peterweissig/project_anhaenger/Skizzen/01_sweethome/export/2020_01_22/gerendert/Ansicht_von_Aussen2.jpg

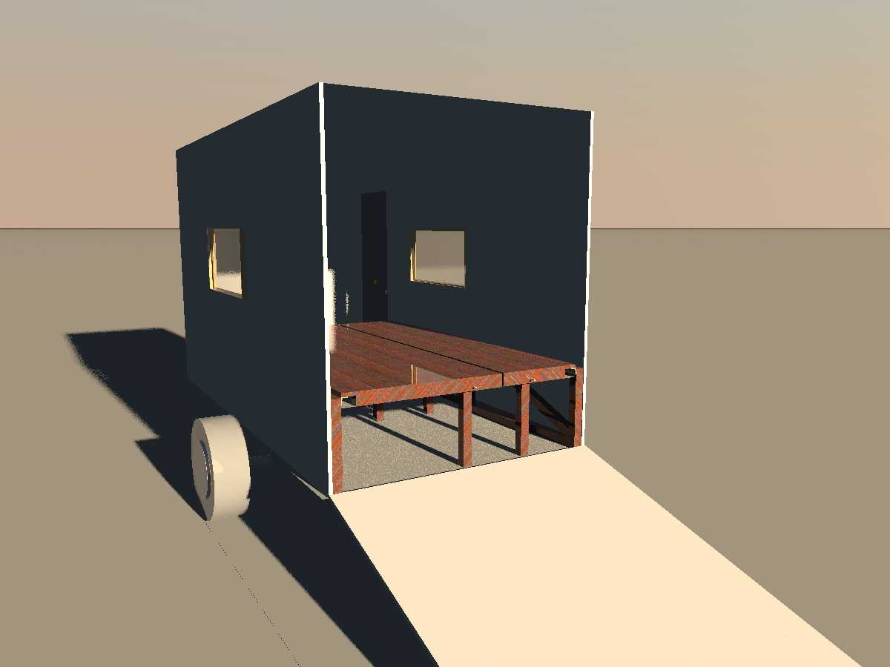
Skizzen/01_sweethome/export/2020_01_22/gerendert/Ansicht_von_Aussen2.jpg
