peterweissig/project_anhaenger/Skizzen/01_sweethome/export/2020_01_22/gerendert/Ansicht_von_Aussen.jpg

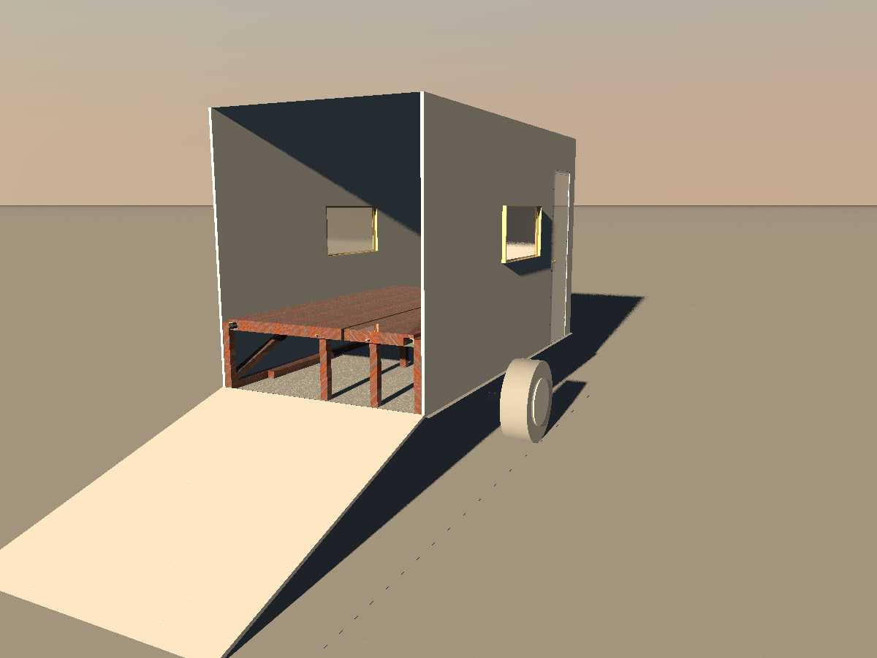
Skizzen/01_sweethome/export/2020_01_22/gerendert/Ansicht_von_Aussen.jpg
