peterweissig/project_anhaenger/Skizzen/01_sweethome/export/2020_01_22/screenshot/Ansicht_von_Aussen_offen.png

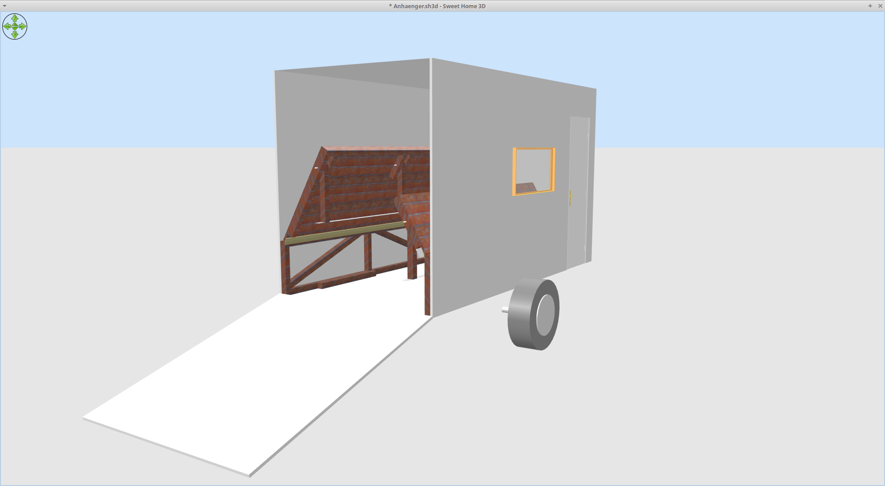
Skizzen/01_sweethome/export/2020_01_22/screenshot/Ansicht_von_Aussen_offen.png
