peterweissig/project_anhaenger/Skizzen/01_sweethome/export/2020_01_22/screenshot/Ansicht_von_Innen_zu.jpg

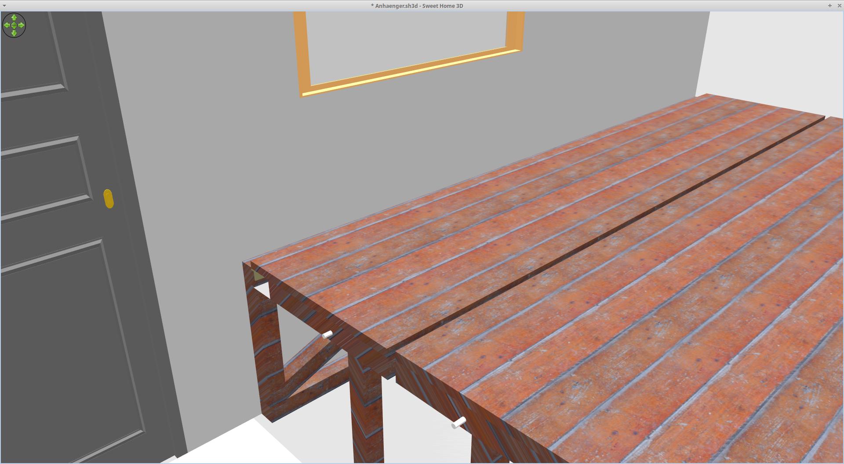
Skizzen/01_sweethome/export/2020_01_22/screenshot/Ansicht_von_Innen_zu.jpg
