peterweissig/project_anhaenger/Skizzen/01_sweethome/export/2020_01_23/aussen2_essen.png

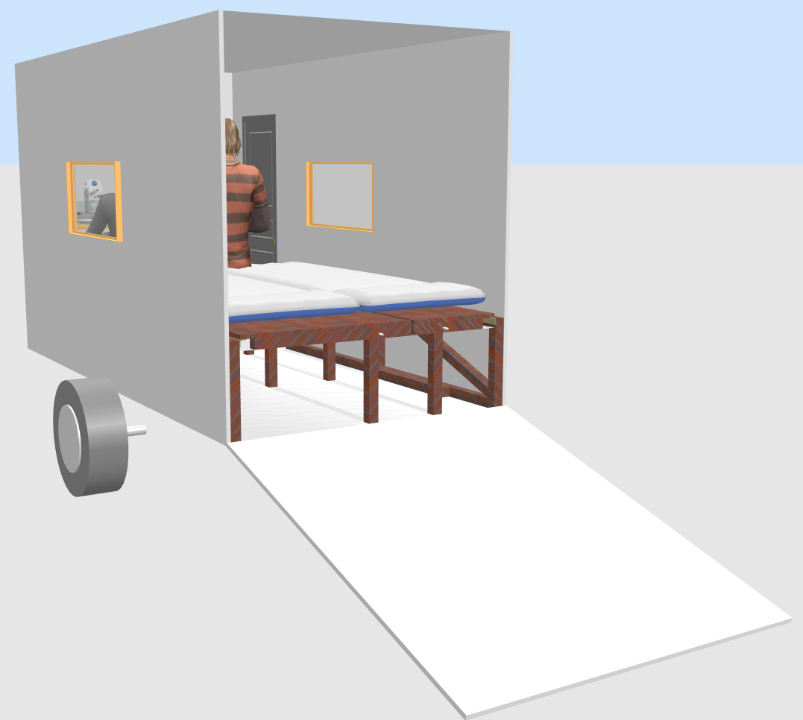
Skizzen/01_sweethome/export/2020_01_23/aussen2_essen.png
