peterweissig/project_anhaenger/Skizzen/02_inventor/export/2020_03_29/anhaenger_gesamt1.png

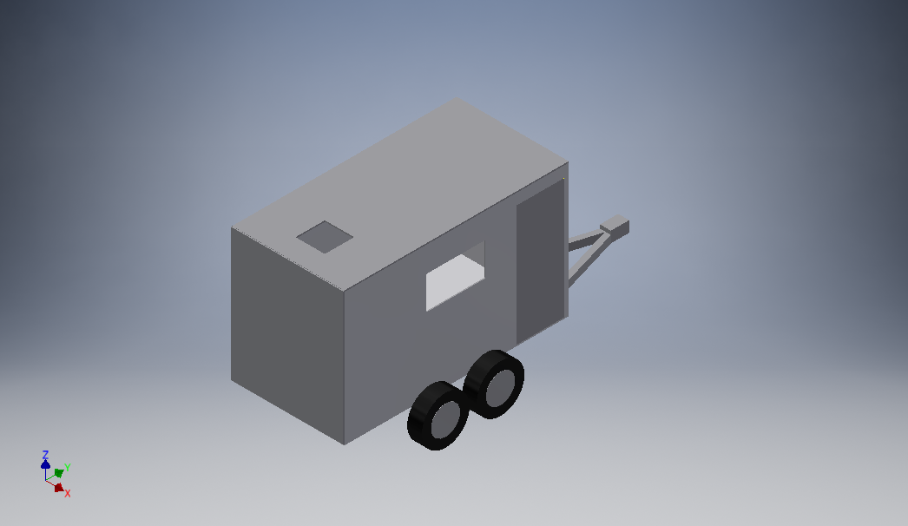
Skizzen/02_inventor/export/2020_03_29/anhaenger_gesamt1.png
