peterweissig/project_anhaenger/Skizzen/02_inventor/export/2020_04_13/anhaenger_gesamt__oben.png

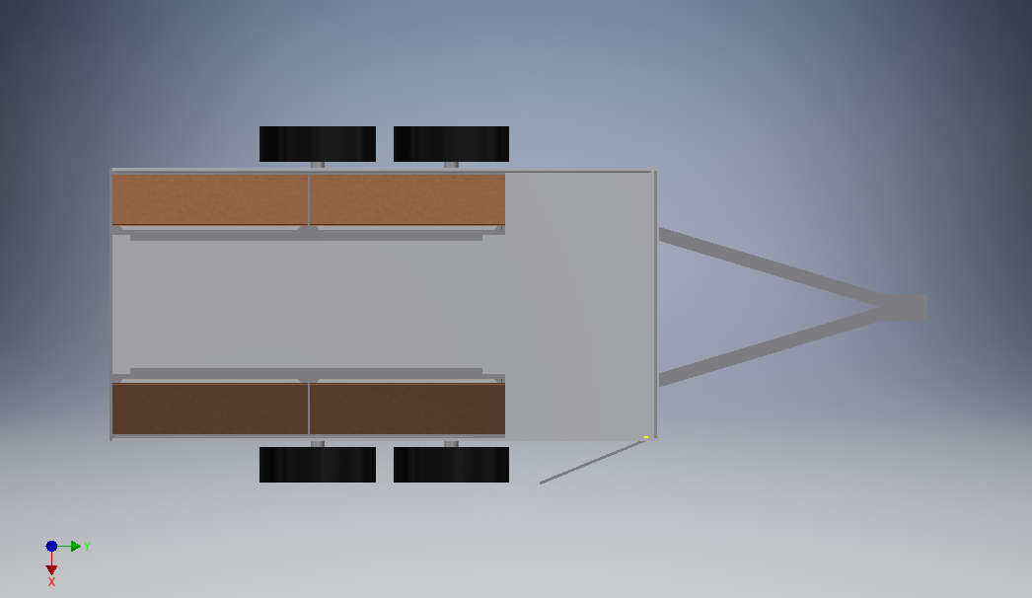
Skizzen/02_inventor/export/2020_04_13/anhaenger_gesamt__oben.png
