peterweissig/project_anhaenger/Skizzen/02_inventor/export/2020_04_19/anhaenger_schraeg2.png

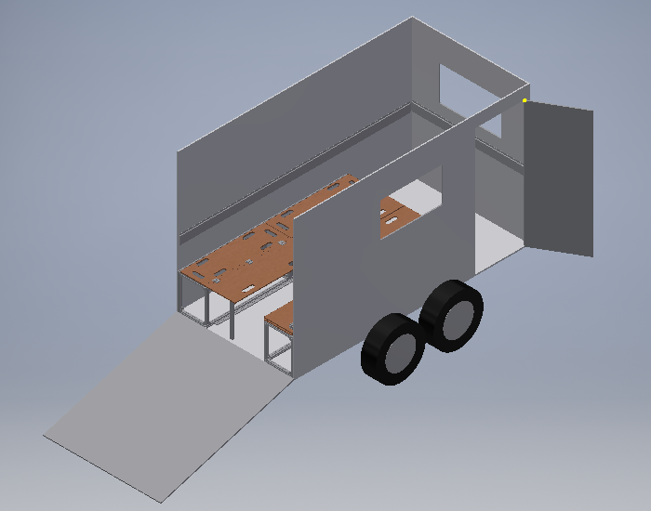
Skizzen/02_inventor/export/2020_04_19/anhaenger_schraeg2.png
